escaner/ufc/doc/pictures/photo_2022-01-12_20-22-10.jpg

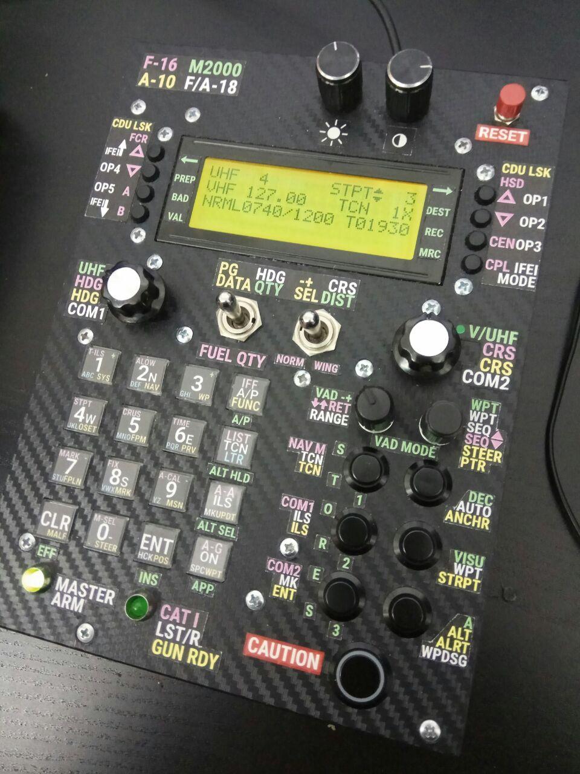
doc/pictures/photo_2022-01-12_20-22-10.jpg
