escaner/ufc/doc/pictures/photo_2022-01-13_23-08-01.jpg

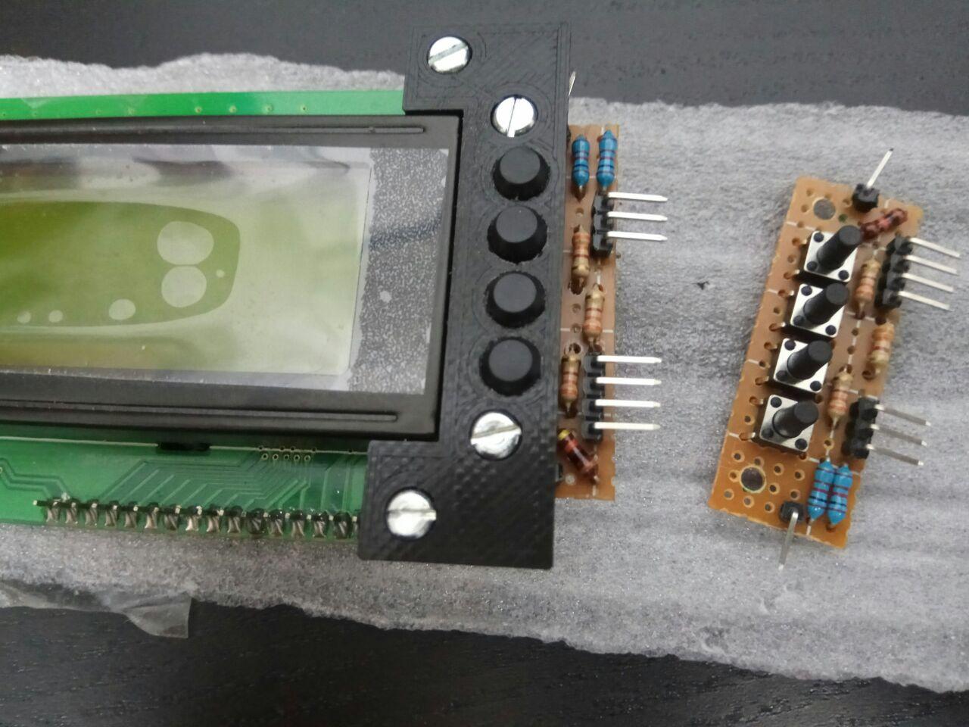
doc/pictures/photo_2022-01-13_23-08-01.jpg
