escaner/ufc/doc/pictures/photo_2022-01-13_23-09-07.jpg

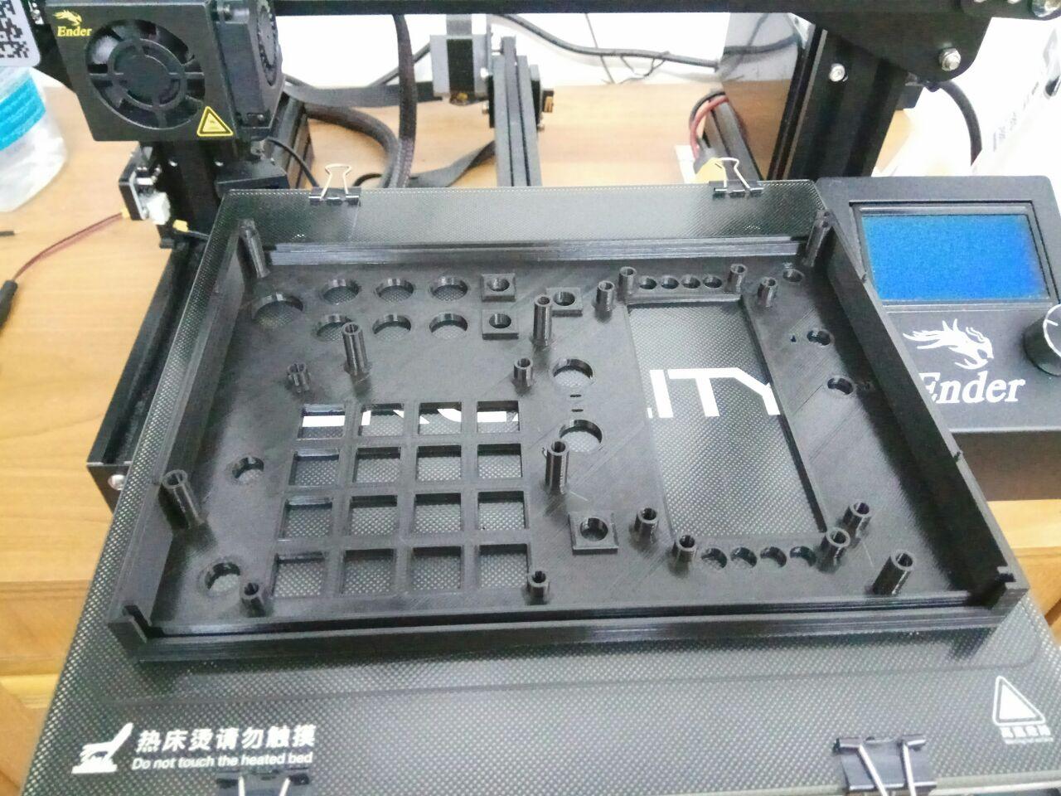
doc/pictures/photo_2022-01-13_23-09-07.jpg
