escaner/ufc/doc/pictures/photo_2022-01-13_23-09-53.jpg

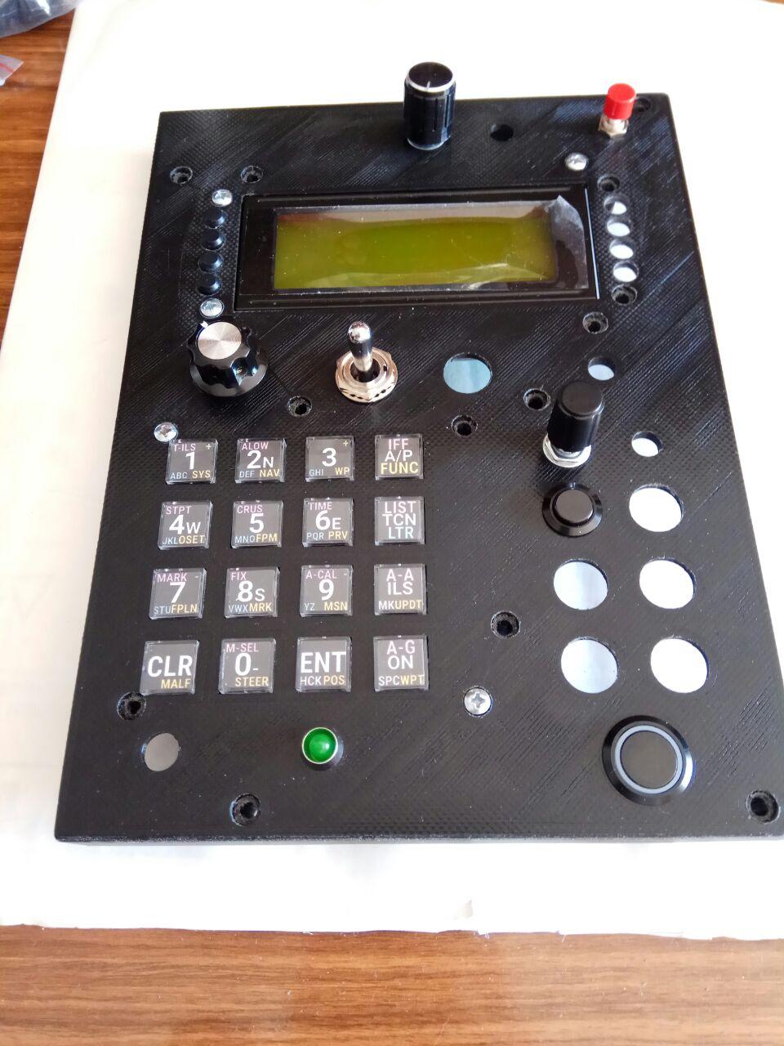
doc/pictures/photo_2022-01-13_23-09-53.jpg
