escaner/ufc/doc/pictures/photo_2022-01-13_23-11-54.jpg

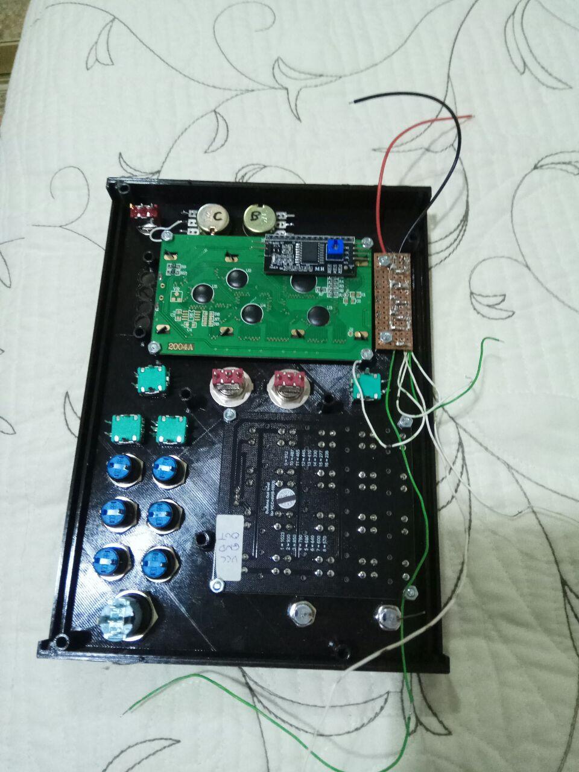
doc/pictures/photo_2022-01-13_23-11-54.jpg
