escaner/ufc/doc/pictures/photo_2022-01-13_23-12-11.jpg

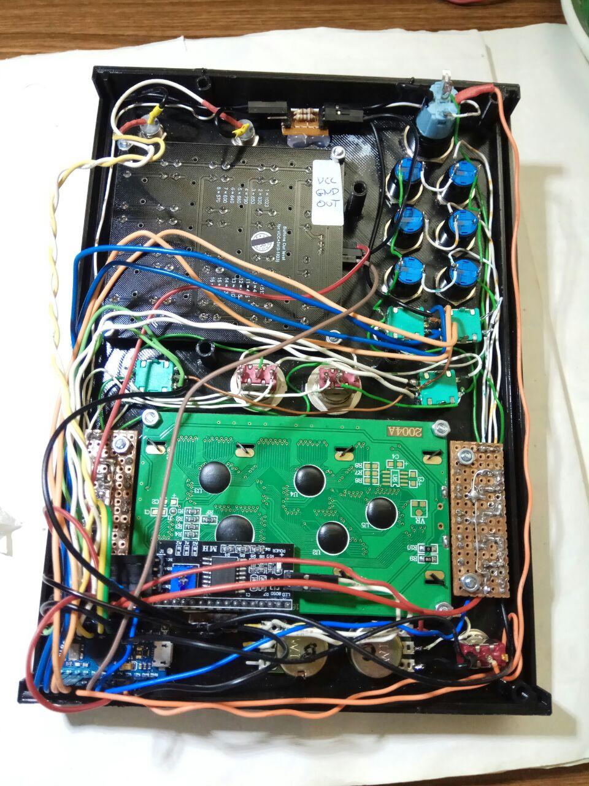
doc/pictures/photo_2022-01-13_23-12-11.jpg
