escaner/ufc/doc/pictures/photo_2022-01-13_23-13-15.jpg

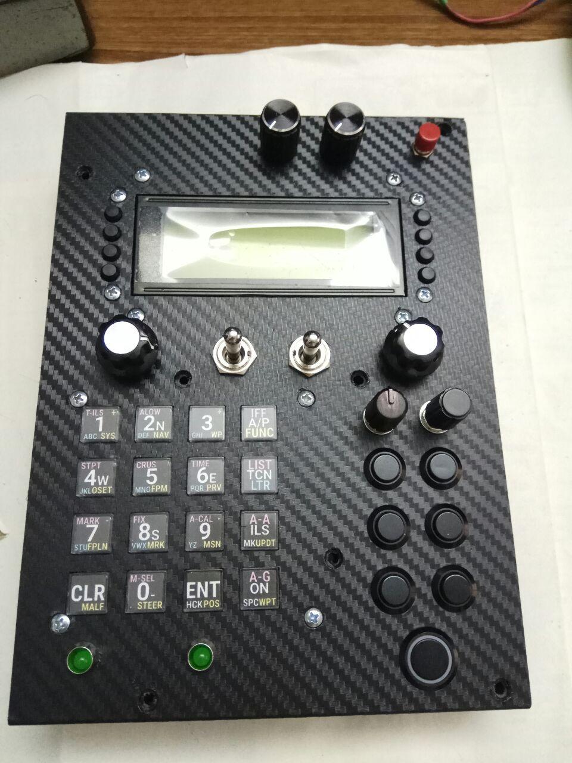
doc/pictures/photo_2022-01-13_23-13-15.jpg
