escaner/ufc/doc/pictures/photo_2022-01-13_23-13-32.jpg

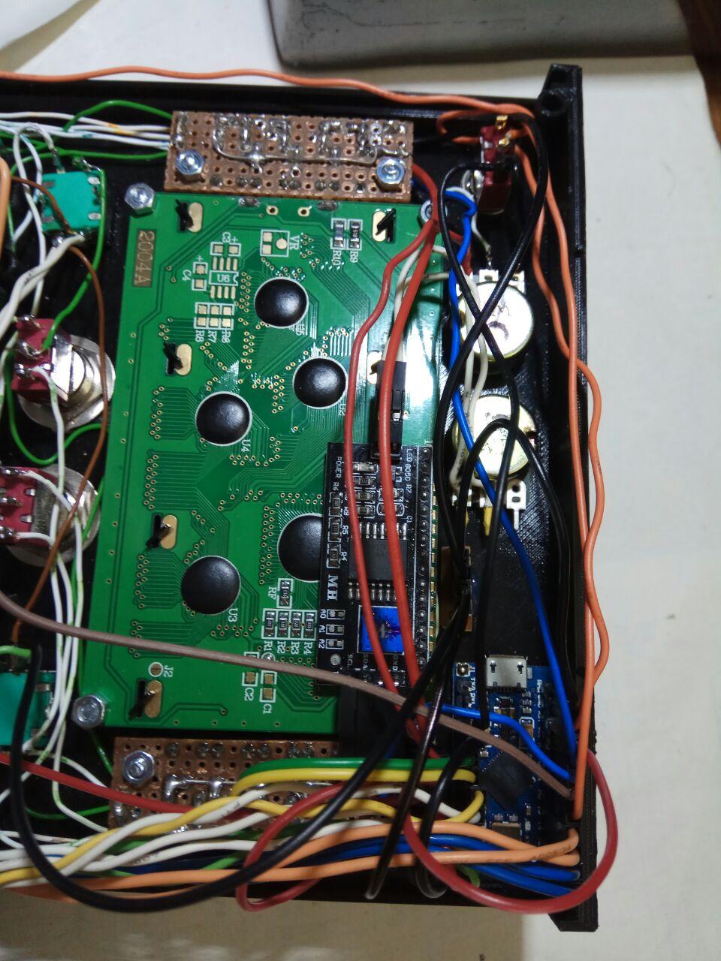
doc/pictures/photo_2022-01-13_23-13-32.jpg
