escaner/ufc/doc/pictures/photo_2022-01-24_09-32-18.jpg

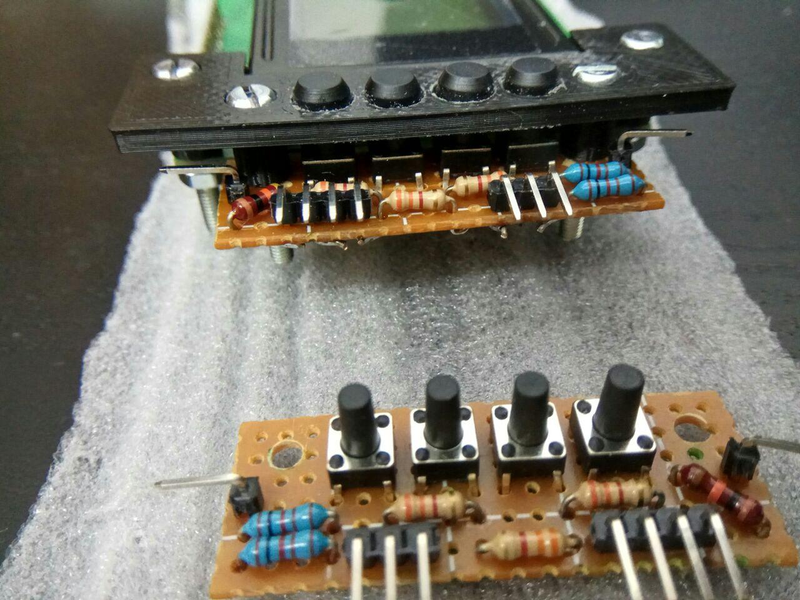
doc/pictures/photo_2022-01-24_09-32-18.jpg
