escaner/ufc/doc/pictures/photo_2022-01-24_09-32-46.jpg

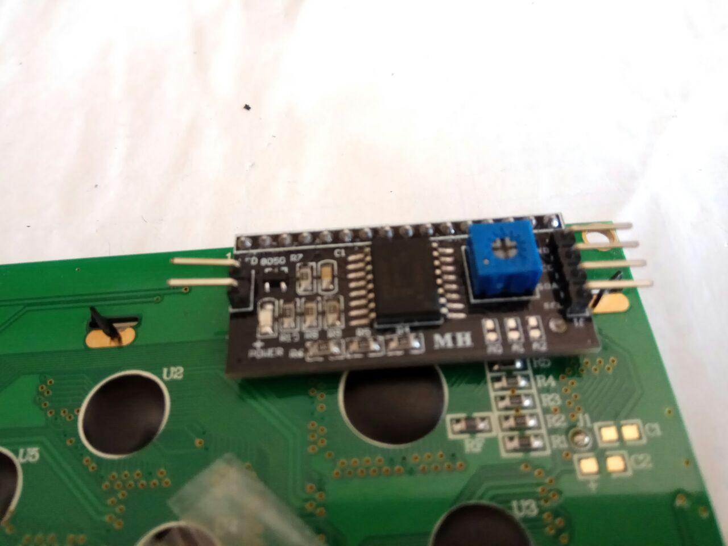
doc/pictures/photo_2022-01-24_09-32-46.jpg
