escaner/ufc/doc/pictures/photo_2022-01-24_09-33-40.jpg

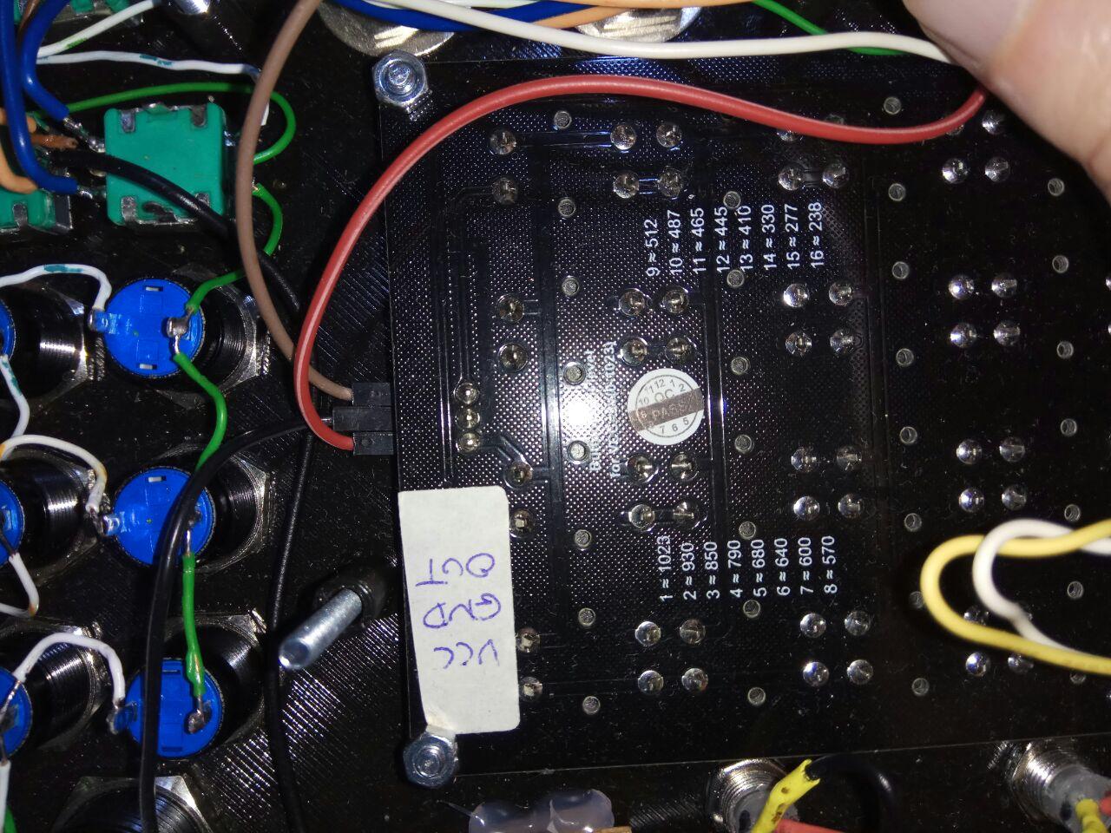
doc/pictures/photo_2022-01-24_09-33-40.jpg
