escaner/ufc/doc/template/num-keypad/a10c-ufc.jpg

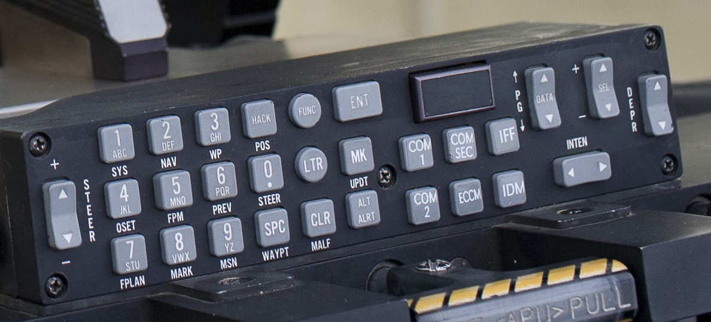
doc/template/num-keypad/a10c-ufc.jpg
