escaner/ufc/doc/template/num-keypad/f16-icp.jpg

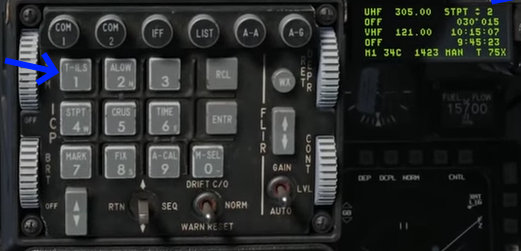
doc/template/num-keypad/f16-icp.jpg
