escaner/ufc/doc/template/num-keypad/m2000-ins.jpg

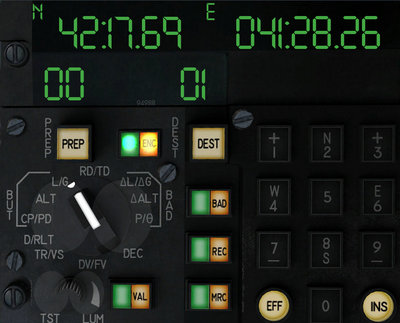
doc/template/num-keypad/m2000-ins.jpg
